rgwch/garage/public/garage-144x144.png

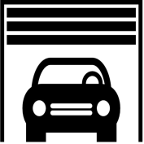
public/garage-144x144.png
