rgwch/garage/public/garage_offen.png

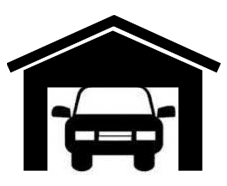
public/garage_offen.png
